b00lduck/si4713-multi-tx/kicad/fm-tx-LCD.kicad_sch

## KiCad design kicad/fm-tx-LCD.kicad_sch (2024-12-23)

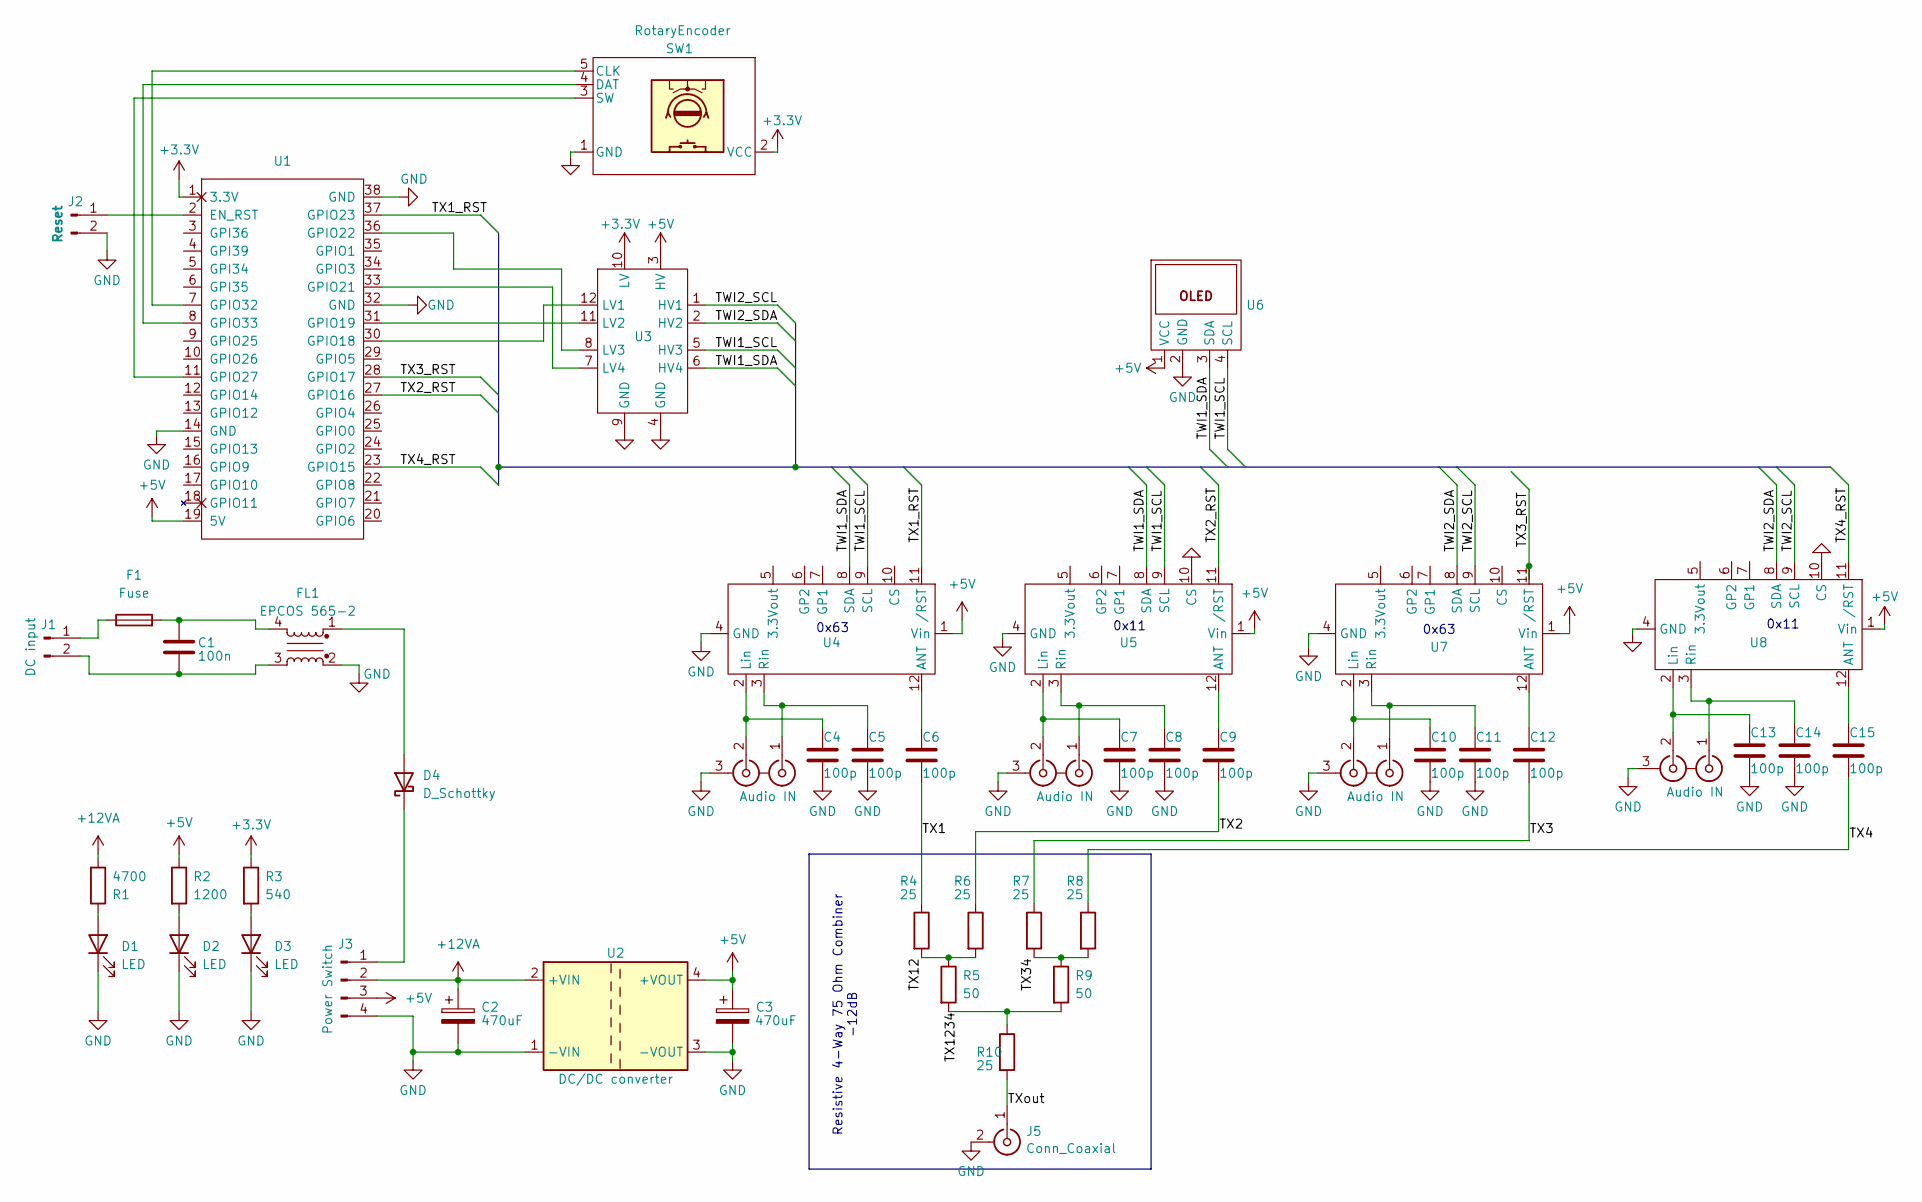
[picture p3: schematic fm-tx-LCD.kicad_sch]

Parts:
C1: 100n; C_0805_2012Metric; LCSC C28233
C2, C3: 470uF; CP_Radial_D8.0mm_P5.00mm
C4, C5, C6, C7, C8, C9, C10, C11, C12, C13, C14, C15: 100p; C_0402_1005Metric; LCSC C1546
D1, D2, D3: LED; LED_D3.0mm
D4: D_Schottky; D_DO-15_P3.81mm_Vertical_AnodeUp
F1: Fuse; Fuseholder_TR5_Littelfuse_No560_No460
FL1: EPCOS 565-2; Choke_Schaffner_RN122-04-28.0x27.0mm
J1: DC input; PinHeader_1x02_P2.54mm_Vertical
J2: Reset; PinHeader_1x02_P2.54mm_Vertical
J3: Power Switch; PinHeader_1x04_P2.54mm_Vertical
J4, J6, J7, J8: Audio IN; cinch
J5: Conn_Coaxial; fstecker
R1: 4700; R_0805_2012Metric; LCSC C17673
R2: 1200; R_0603_1608Metric; LCSC C22765
R3: 540; R_0603_1608Metric; LCSC C23204
R4, R6, R7, R8, R10: 25; R_0805_2012Metric; LCSC C2828760
R5, R9: 50; R_0402_1005Metric; LCSC C3015747
SW1: RotaryEncoder; PinHeader_1x05_P2.54mm_Vertical
U1: esp32_38_pins-custom_library; ESP32-DevKitC
U2: DC/DC converter; lm2596_module
U3: i2c_levelshifter
U4, U5, U7, U8: si4713_breakout
U6: PinHeader_1x04_P2.54mm_Vertical

Connections:
+3.3V: R3.1, SW1.2 (VCC), U1.1 (3.3V), U3.10 (LV)
+5V: C3.1, J3.3, R2.1, U1.19 (5V), U2.4 (+VOUT), U3.3 (HV), U4.1 (Vin), U5.1 (Vin), U6.1 (VCC), U7.1 (Vin), U8.1 (Vin)
+12VA: C2.1, J3.2, R1.2, U2.2 (+VIN)
GND: C2.2, C3.2, C4.2, C5.2, C7.2, C8.2, C10.2, C11.2, C13.2, C14.2, D1.1 (K), D2.1 (K), D3.1 (K), FL1.2, J2.2, J3.4, J4.3 (EXT), J5.2 (Ext), J6.3 (EXT), J7.3 (EXT), J8.3 (EXT), SW1.1 (GND), U1.14 (GND), U1.32 (GND), U1.38 (GND), U2.1 (-VIN), U2.3 (-VOUT), U3.4 (GND), U3.9 (GND), U4.4 (GND), U5.4 (GND), U5.10 (CS), U6.2 (GND), U7.4 (GND), U8.4 (GND), U8.10 (CS)
unnamed: C1.1, F1.2, FL1.4
unnamed: C1.2, FL1.3, J1.2
unnamed: C4.1, J4.2 (IN2), U4.2 (Lin)
unnamed: C5.1, J4.1 (IN1), U4.3 (Rin)
unnamed: C6.1, U4.12 (ANT)
unnamed: C7.1, J6.2 (IN2), U5.2 (Lin)
unnamed: C8.1, J6.1 (IN1), U5.3 (Rin)
unnamed: C9.1, U5.12 (ANT)
unnamed: C10.1, J7.2 (IN2), U7.2 (Lin)
unnamed: C11.1, J7.1 (IN1), U7.3 (Rin)
unnamed: C12.1, U7.12 (ANT)
unnamed: C13.1, J8.2 (IN2), U8.2 (Lin)
unnamed: C14.1, J8.1 (IN1), U8.3 (Rin)
unnamed: C15.1, U8.12 (ANT)
unnamed: D1.2 (A), R1.1
unnamed: D2.2 (A), R2.2
unnamed: D3.2 (A), R3.2
unnamed: D4.1 (K), J3.1
unnamed: D4.2 (A), FL1.1
unnamed: F1.1, J1.1
unnamed: J2.1, U1.2 (EN_RST)
unnamed: SW1.3 (SW), U1.11 (GPIO27)
unnamed: SW1.4 (DAT), U1.8 (GPIO33)
unnamed: SW1.5 (CLK), U1.7 (GPIO32)
unnamed: U1.30 (GPIO18), U3.12 (LV1)
unnamed: U1.31 (GPIO19), U3.11 (LV2)
unnamed: U1.33 (GPIO21), U3.7 (LV4)
unnamed: U1.36 (GPIO22), U3.8 (LV3)
TWI1_SCL: U3.5 (HV3), U4.9 (SCL), U5.9 (SCL), U6.4 (SCL)
TWI1_SDA: U3.6 (HV4), U4.8 (SDA), U5.8 (SDA), U6.3 (SDA)
TWI2_SCL: U3.1 (HV1), U7.9 (SCL), U8.9 (SCL)
TWI2_SDA: U3.2 (HV2), U7.8 (SDA), U8.8 (SDA)
TX1: C6.2, R4.1
TX1_RST: U1.37 (GPIO23), U4.11 (/RST)
TX2: C9.2, R6.1
TX2_RST: U1.27 (GPIO16), U5.11 (/RST)
TX3: C12.2, R7.1
TX3_RST: U1.28 (GPIO17), U7.11 (/RST)
TX4: C15.2, R8.1
TX4_RST: U1.23 (GPIO15), U8.11 (/RST)
TX12: R4.2, R5.1, R6.2
TX34: R7.2, R8.2, R9.1
TX1234: R5.2, R9.2, R10.1
TXout: J5.1 (In), R10.2

Notes on the sheet:
Resistive 4-Way 75 Ohm Combiner -12dB
0x11
0x63
