b00lduck/si4713-multi-tx/kicad/fm-tx.kicad_sch

## KiCad design kicad/fm-tx.kicad_sch (2024-04-12, an earlier design)

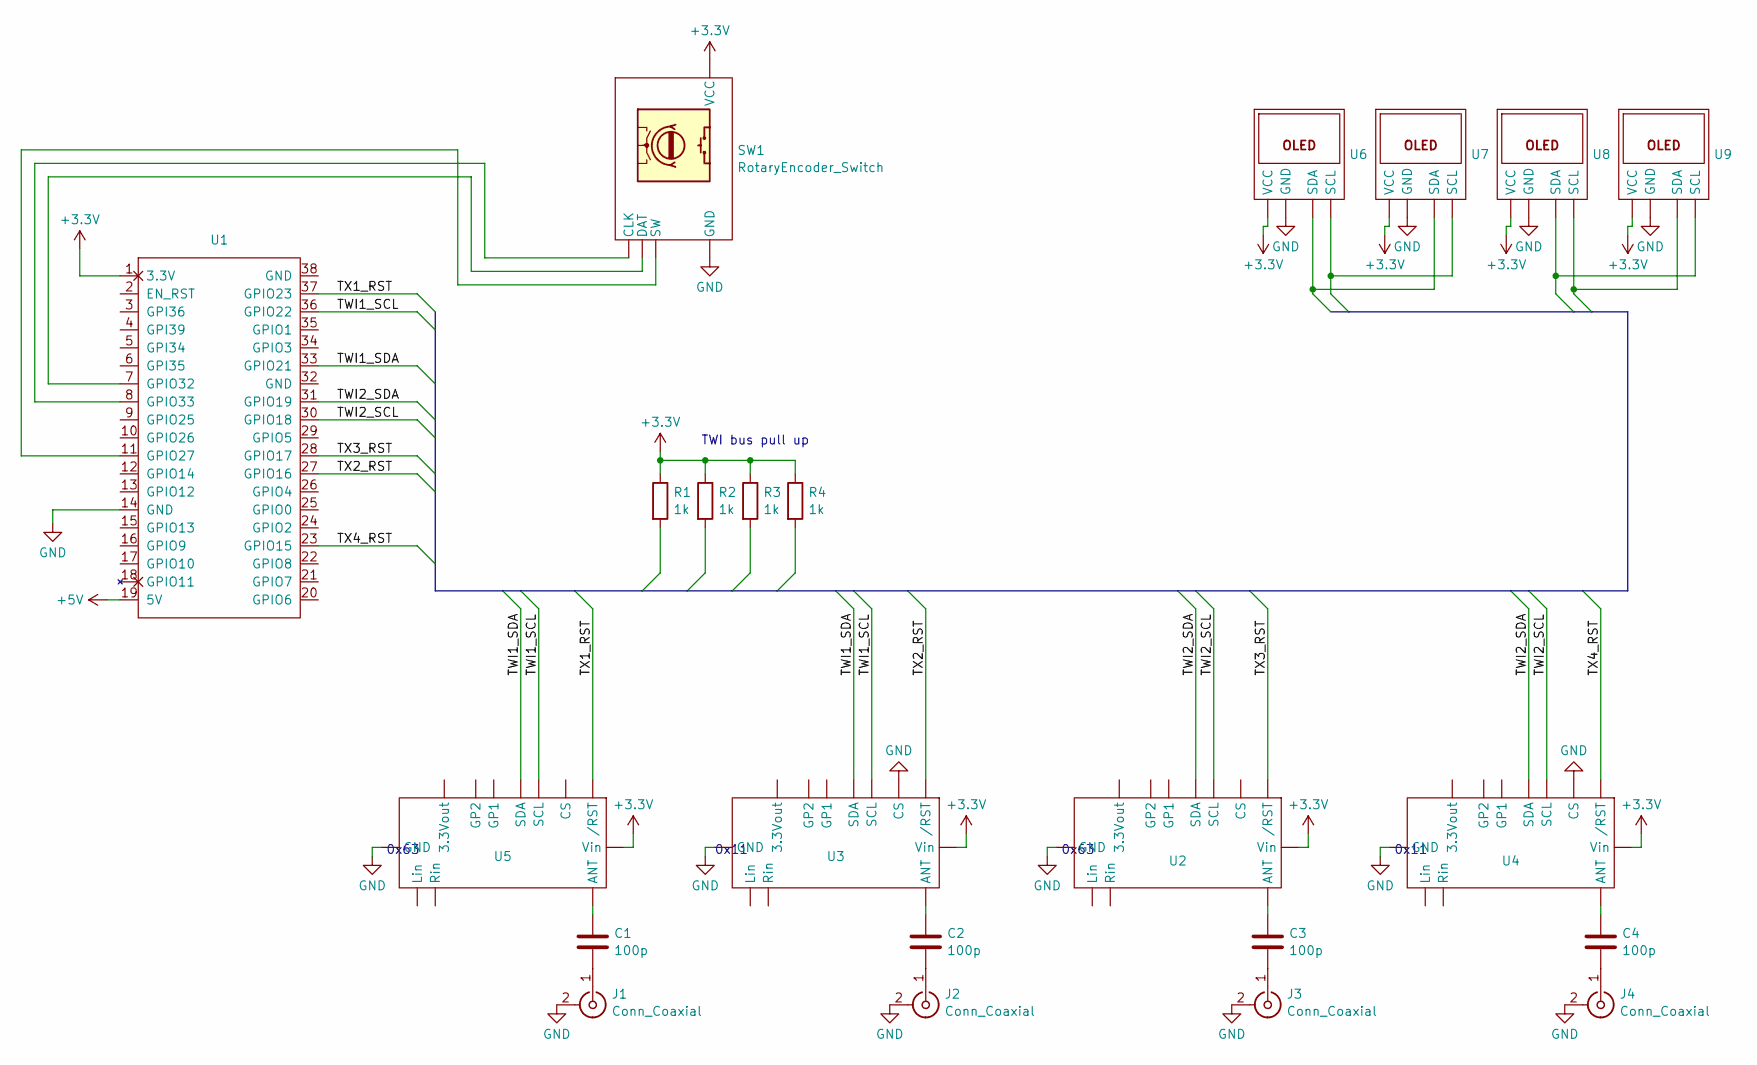
[picture p4: schematic fm-tx.kicad_sch]

Parts:
C1, C2, C3, C4: 100p
J1, J2, J3, J4: Conn_Coaxial
R1, R2, R3, R4: 1k
SW1: RotaryEncoder_Switch
U1: esp32_38_pins-custom_library; esp32_devkitv4_38pin
U2, U3, U4, U5, U6, U7, U8, U9: (no value)

Connections:
+3.3V: R1.1, R2.1, R3.1, R4.1, SW1., U1.1 (3.3V), U2., U3., U4., U5., U6., U7., U8., U9.
+5V: U1.19 (5V)
GND: J1.2 (Ext), J2.2 (Ext), J3.2 (Ext), J4.2 (Ext), SW1., U1.14 (GND), U2., U3., U4., U5., U6., U7., U8., U9.
unnamed: C1.1, U5.
unnamed: C1.2, J1.1 (In)
unnamed: C2.1, U3.
unnamed: C2.2, J2.1 (In)
unnamed: C3.1, U2.
unnamed: C3.2, J3.1 (In)
unnamed: C4.1, U4.
unnamed: C4.2, J4.1 (In)
unnamed: SW1., U1.7 (GPIO32), U1.8 (GPIO33), U1.11 (GPIO27)
unnamed: U6., U7.
unnamed: U8., U9.
TWI1_SCL: U1.36 (GPIO22), U3., U5.
TWI1_SDA: U1.33 (GPIO21), U3., U5.
TWI2_SCL: U1.30 (GPIO18), U2., U4.
TWI2_SDA: U1.31 (GPIO19), U2., U4.
TX1_RST: U1.37 (GPIO23), U5.
TX2_RST: U1.27 (GPIO16), U3.
TX3_RST: U1.28 (GPIO17), U2.
TX4_RST: U1.23 (GPIO15), U4.

Notes on the sheet:
TWI bus pull up
0x11
0x63
