b00lduck/si4713-multi-tx/src/State.h

#pragma once
#include "config.h"
#include <Arduino.h>

class ChannelState {
    public:
        ChannelState();
        void load(uint8_t id);
        void save();
    
        // kHz/10, 8750-10800
        uint16_t freq;
        
        // Programme Service Name
        char ps[9];

        // dBuV, 88-115 max (120 uncalibrated)
        uint8_t txPower;

        // enable TX
        bool enabled;

    private:
        uint8_t id;
};

class State {

    public:
        State();
        void load(uint8_t numtx);
        void save(uint8_t numtx);

        ChannelState channelState[MAX_NUM_TX];

};
