b00lduck/si4713-multi-tx/src/charset.h

#include <Arduino.h>

uint8_t bar1[] = { 
  0b11111,
  0b10000,
  0b10000,
  0b10000,
  0b10000,
  0b10000,
  0b10000,
  0b11111
};

uint8_t bar2[] = { 
  0b11111,
  0b00000,
  0b00000,
  0b00000,
  0b00000,
  0b00000,
  0b00000,
  0b11111
};

uint8_t bar3[] = { 
  0b11111,
  0b00001,
  0b00001,
  0b00001,
  0b00001,
  0b00001,
  0b00001,
  0b11111
};

uint8_t enabledOn[] = { 
  0b00000,
  0b11111,
  0b11111,
  0b11111,
  0b11111,
  0b11111,
  0b11111,
  0b00000
};


uint8_t lvl1[] = { 
  0b00000,
  0b00000,
  0b00000,
  0b00000,
  0b00000,
  0b00000,
  0b00000,
  0b01110
};

uint8_t lvl2[] = { 
  0b00000,
  0b00000,
  0b00000,
  0b00000,
  0b00000,
  0b00000,
  0b01110,
  0b01110
};

uint8_t lvl3[] = { 
  0b00000,
  0b00000,
  0b00000,
  0b00000,
  0b00000,
  0b01110,
  0b01110,
  0b01110
};

uint8_t lvl4[] = { 
  0b00000,
  0b00000,
  0b00000,
  0b00000,
  0b01110,
  0b01110,
  0b01110,
  0b01110
};

uint8_t lvl5[] = { 
  0b00000,
  0b00000,
  0b00000,
  0b01110,
  0b01110,
  0b01110,
  0b01110,
  0b01110
};

uint8_t lvl6[] = { 
  0b00000,
  0b00000,
  0b01110,
  0b01110,
  0b01110,
  0b01110,
  0b01110,
  0b01110
};

uint8_t lvl7[] = { 
  0b00000,
  0b01110,
  0b01110,
  0b01110,
  0b01110,
  0b01110,
  0b01110,
  0b01110
};
